4ms/4ms-kicad-lib/3dmodels/c-2267077-2-a-3d.step

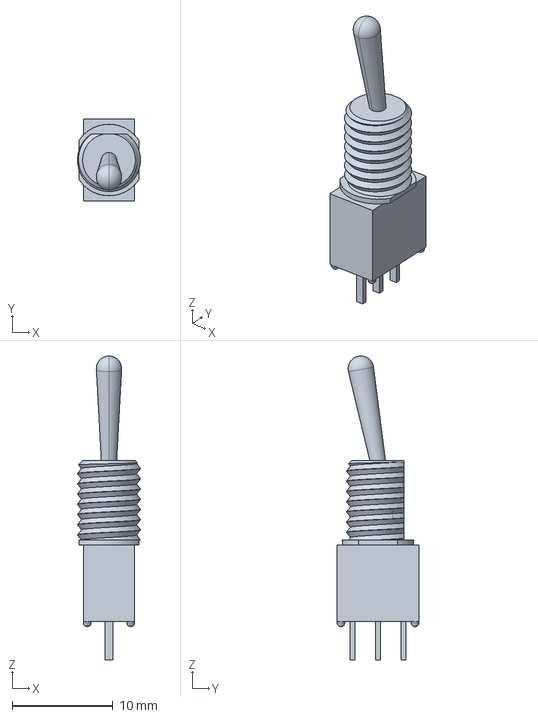
[picture p15: CAD file, 2019-01-21]
3dmodels/c-2267077-2-a-3d.step
6.26 x 8.13 x 30.2 mm
