4ms/4ms-kicad-lib/3dmodels/TSS-108-01-G-D.stp

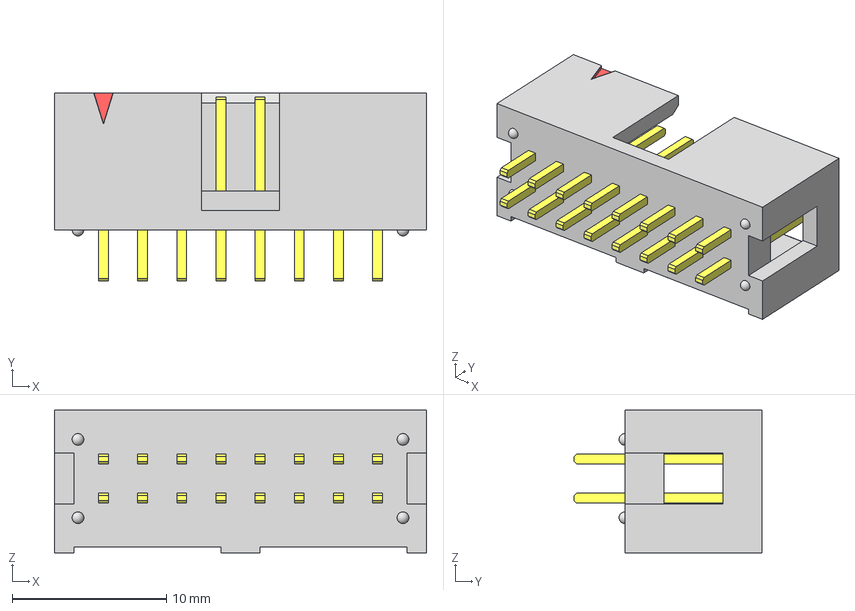
[picture p16: CAD file, 2018-06-27]
3dmodels/TSS-108-01-G-D.stp
24.1 x 12.2 x 9.27 mm
_TSS-108-01-D_header
_TSS-First_Position_Indicator
_T-1S6-08-01-D__
