4ms/4ms-kicad-lib/3dmodels/CUI_PJ-064A.STL

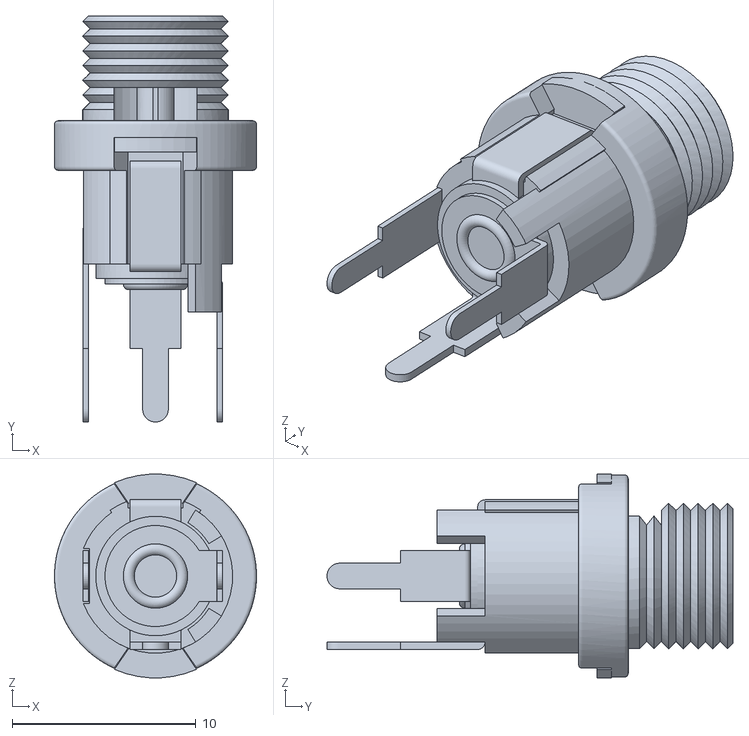
[picture p17: CAD file, 2018-02-10]
3dmodels/CUI_PJ-064A.STL
11.0 x 22.1 x 11.1
