4ms/4ms-kicad-lib/3dmodels/CUI_PJ-066A.STL

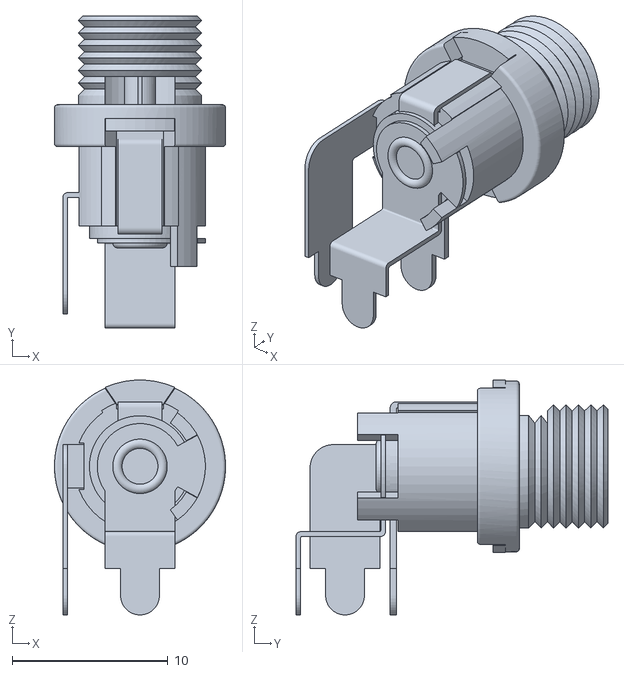
[picture p18: CAD file, 2018-02-10]
3dmodels/CUI_PJ-066A.STL
11.0 x 20.1 x 15.1
