4ms/4ms-kicad-lib/schematic-blocks/jacksense_input_monojack.sch

## KiCad design schematic-blocks/jacksense_input_monojack.sch (2020-12-22)

Schematic: jacksense_input_monojack.sch

Parts:
D33: BAT54S; SOT23-3_PO132; Part Number BAT54S-7-F; JLCPCB ID C83574
R1: 4.7M_0603; R_0603; Part Number RC0603FR-074M7L
R2: 4.7k_0603; R_0603; Part Number RC0603FR-074K7L
