4ms/4ms-kicad-lib/schematic-blocks/uc_power_5V.sch

## KiCad design schematic-blocks/uc_power_5V.sch (2019-08-02)

Schematic: uc_power_5V.sch

Parts:
C1: 22uF; C_1210; Part number UMK325BJ106KMHP
C2: 0.1uF; C_0603
C3: 47pF; C_0603; Part number 885012005078
C4: 22uF; C_0805; Part number JMK212ABJ226MD-T
C5: 10uF; C_0603; Part number GRM188R61A106KE69D
L1: 15uH; COIL_5040; Part number SRN5040TA-150M
R1: 100k; R_0603
R2: 75k; R_0603
R3: 40.2k; R_0603
R4: 7.68k; R_0603
U1: AP65211A; TSOT-23-6
